eez-open/psu-tester/EEZ tester r1B3 (bottom).png

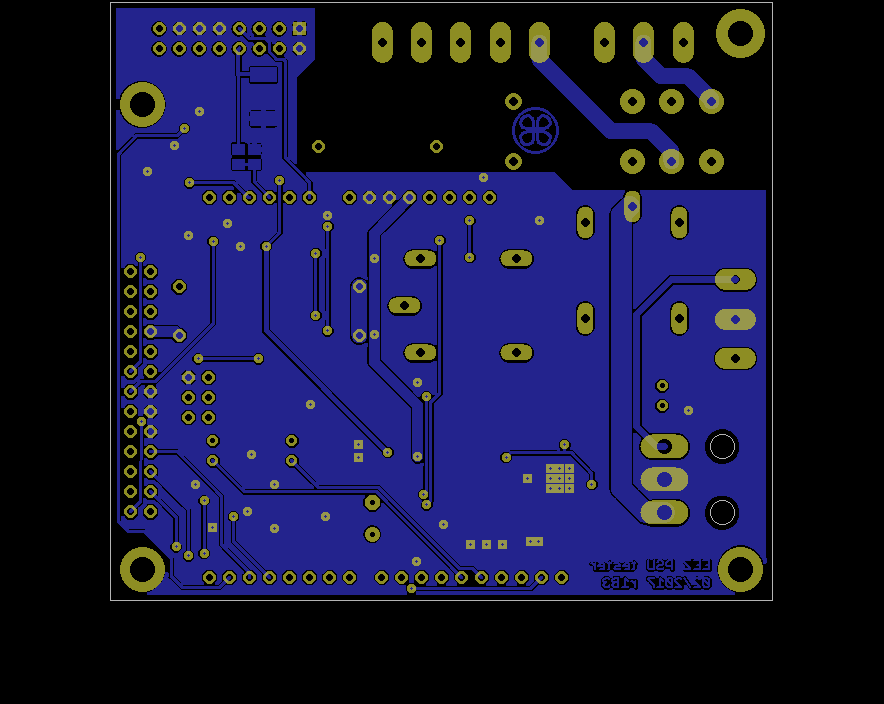
EEZ tester r1B3 (bottom).png
